wikihouseproject/Wren/Images/End-wall-01.png

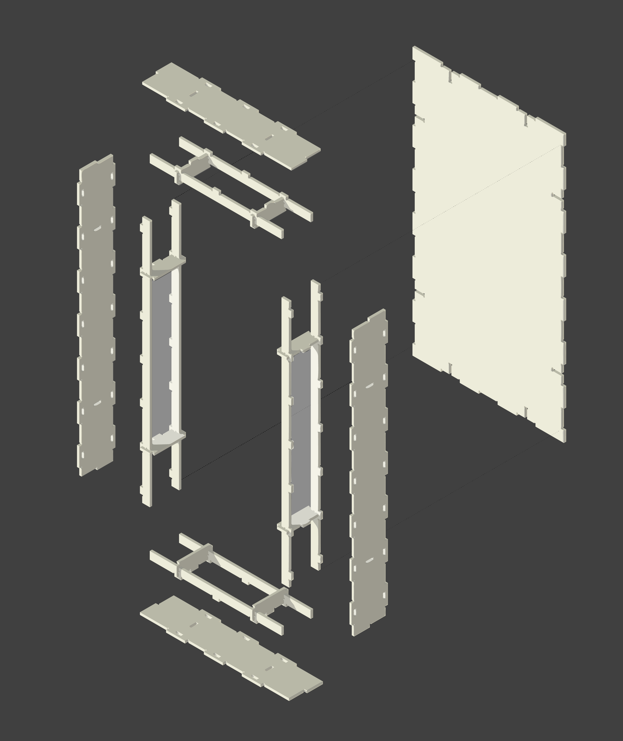
Images/End-wall-01.png
