wikihouseproject/Wren/Images/End-wall-02.png

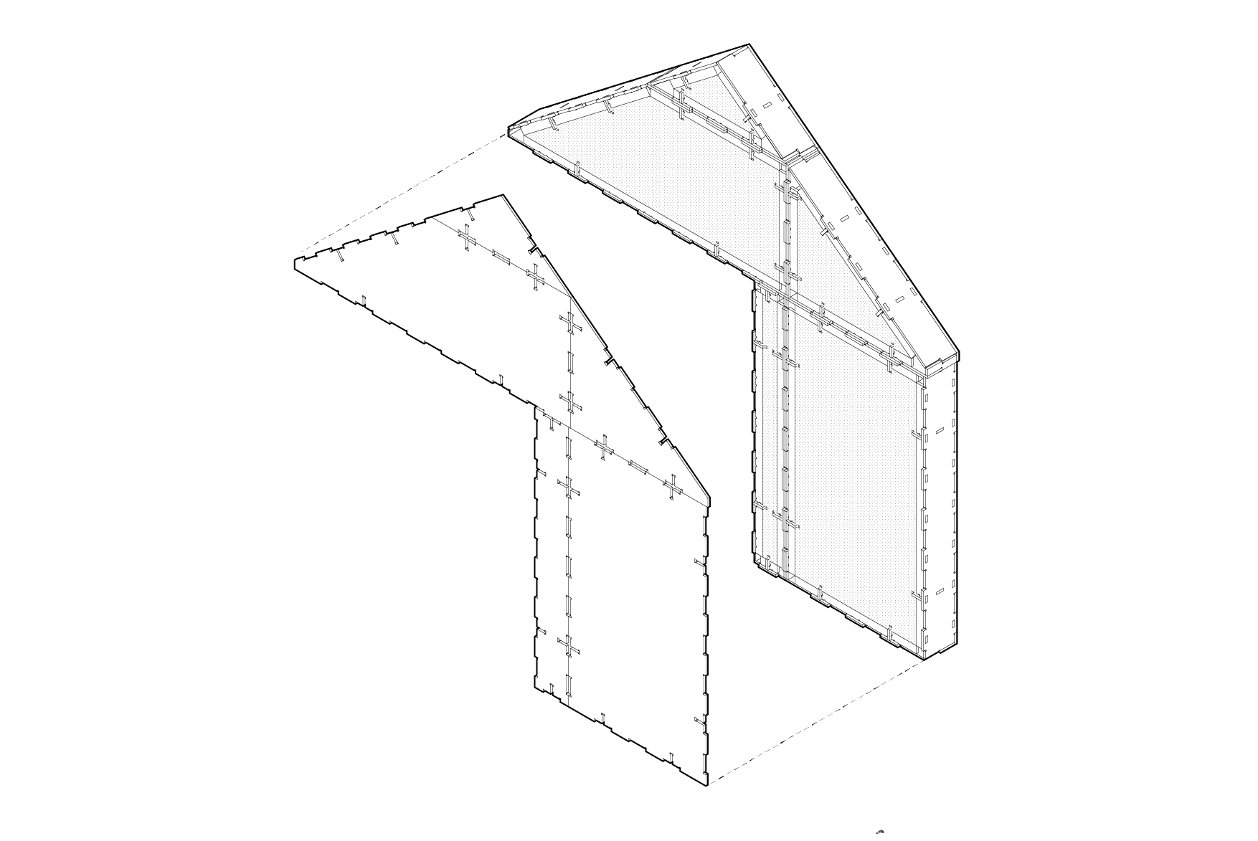
Images/End-wall-02.png
