wikihouseproject/Wren/Images/FIn-01.png

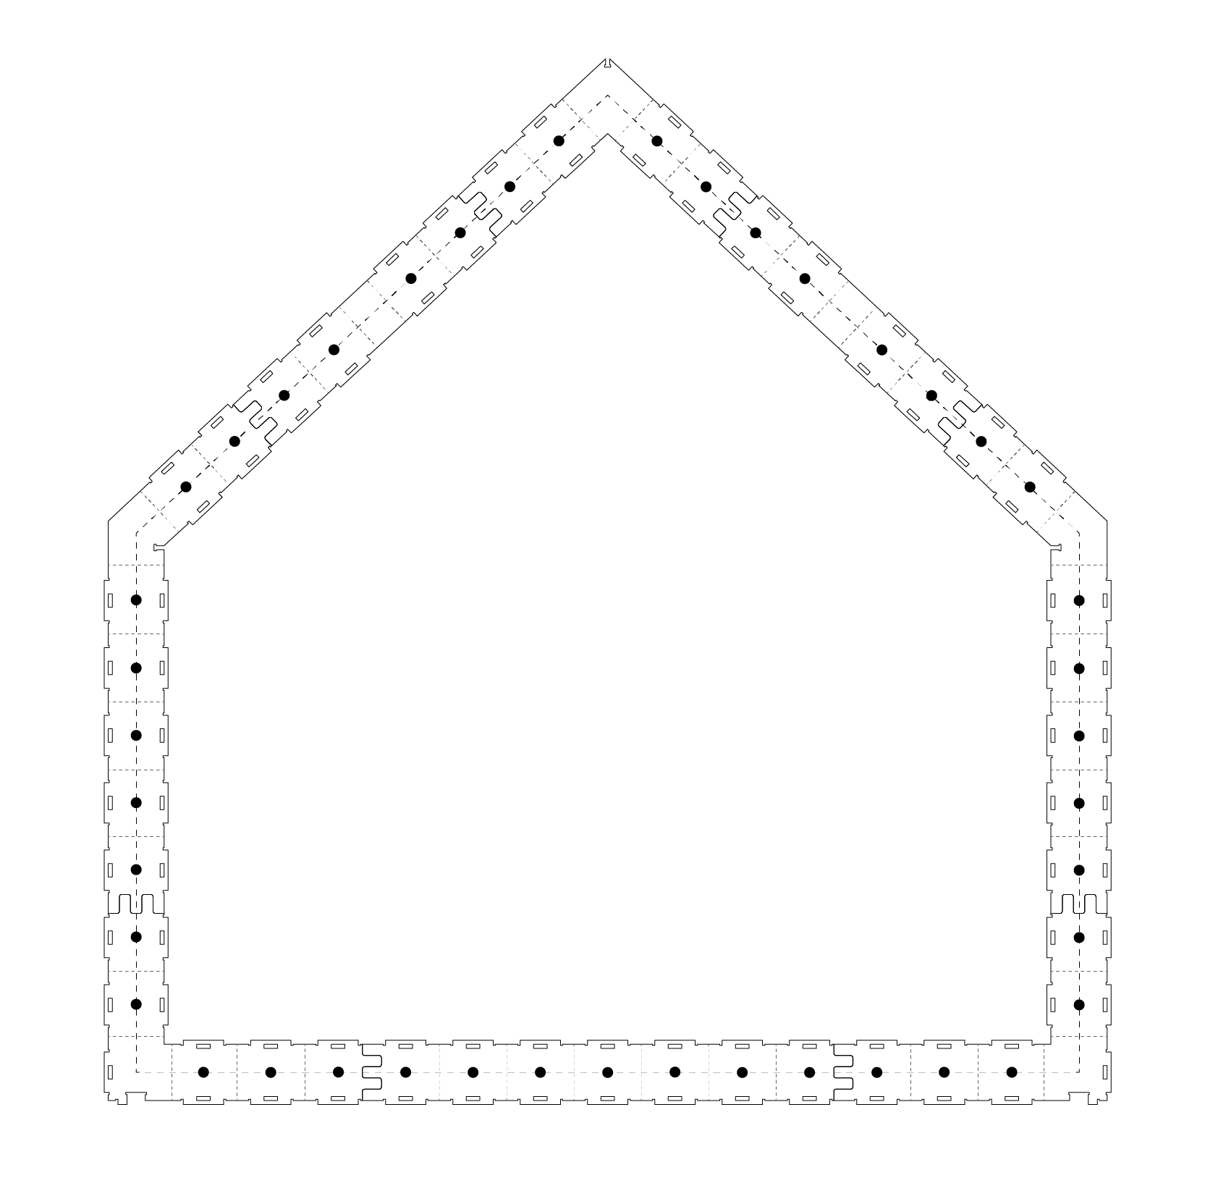
Images/FIn-01.png
