wikihouseproject/Wren/Images/Fin-02.png

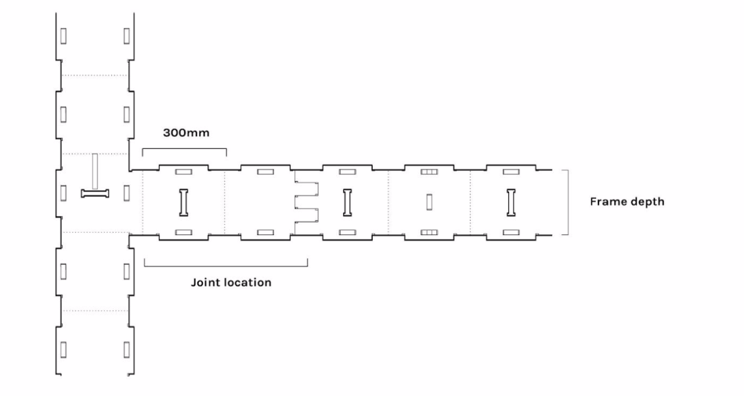
Images/Fin-02.png
