wikihouseproject/Wren/Images/Form-01.png

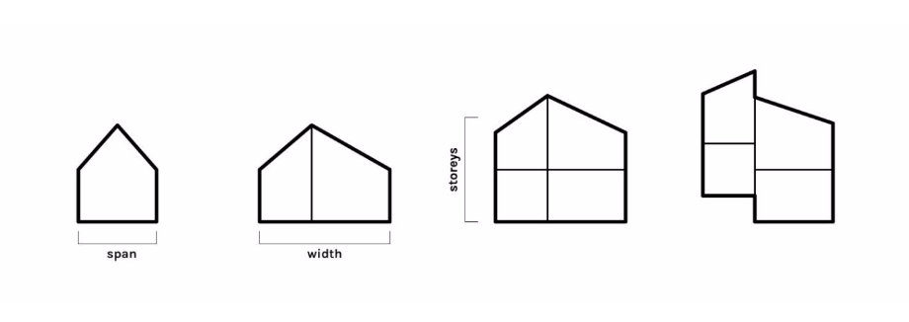
Images/Form-01.png
