wikihouseproject/Wren/Images/Frame-01.png

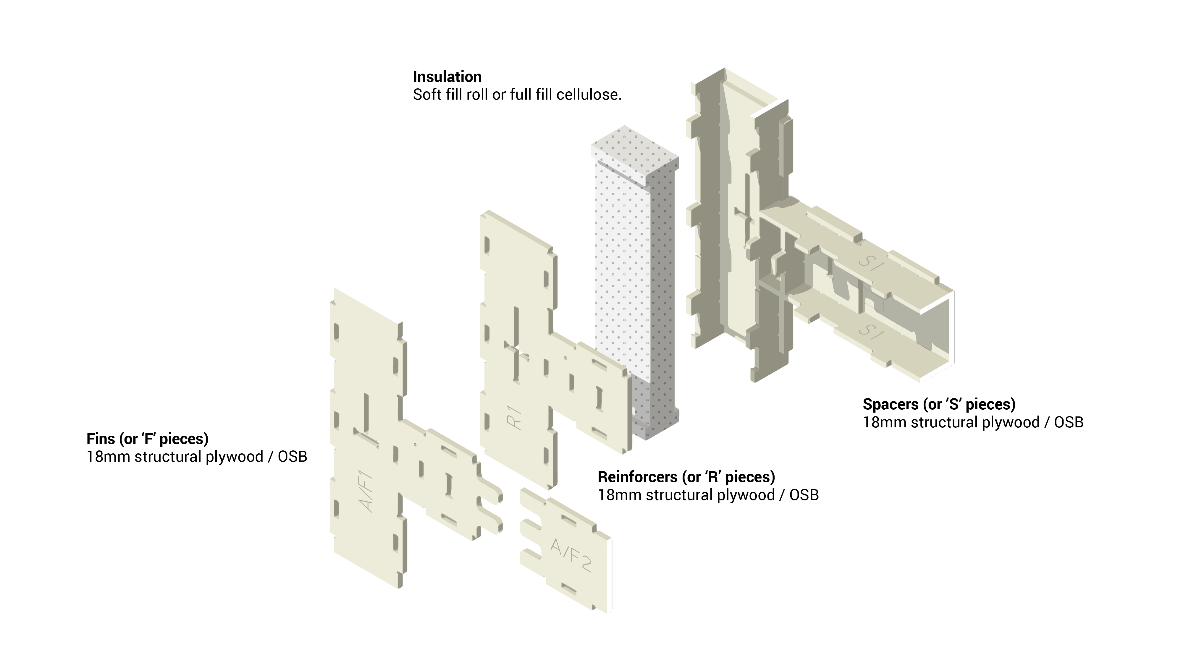
Images/Frame-01.png
