wikihouseproject/Wren/Images/Important.png

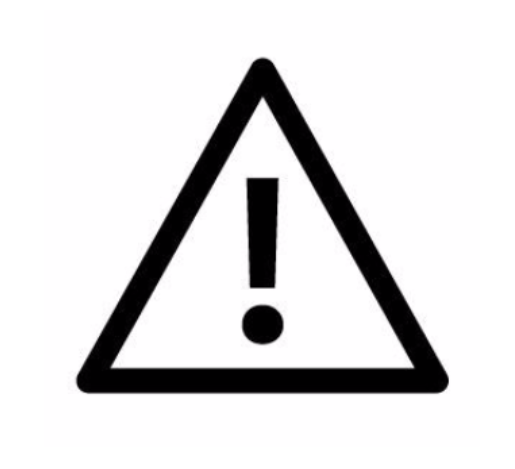
Images/Important.png
