wikihouseproject/Wren/Images/Openings-02.png

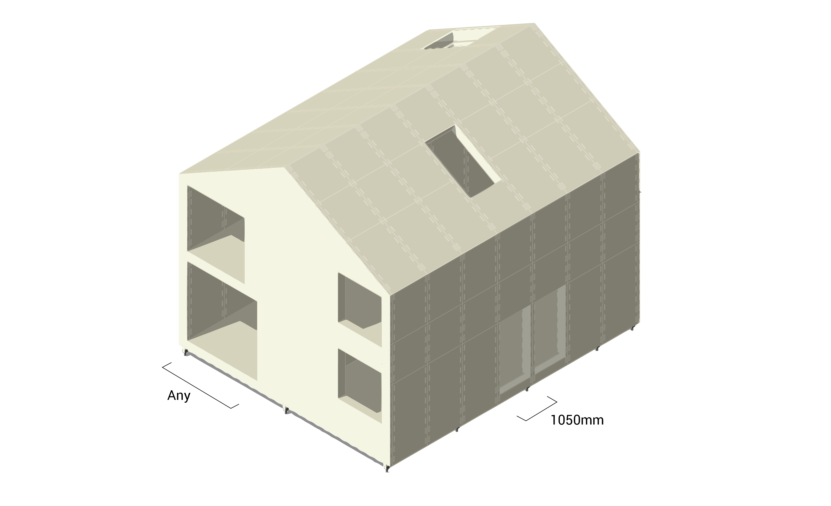
Images/Openings-02.png
