wikihouseproject/Wren/Images/Principles-01.png

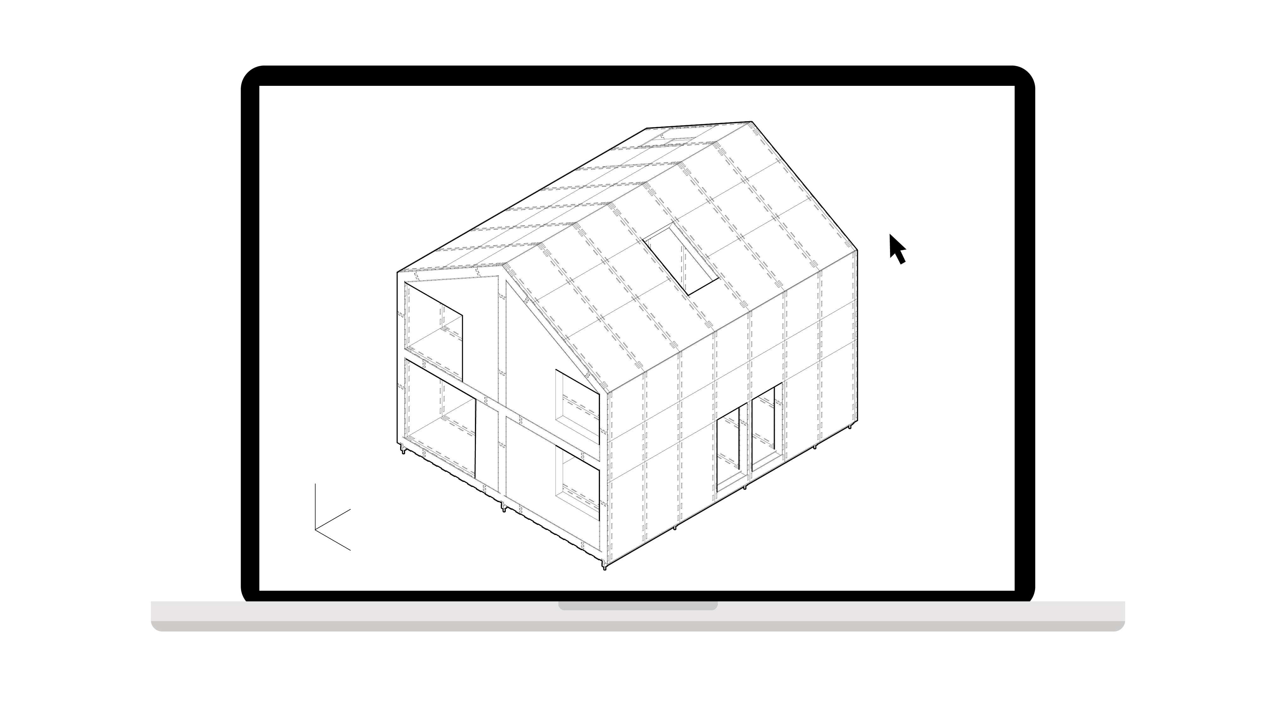
Images/Principles-01.png
