wikihouseproject/Wren/Images/Sheathing-01.png

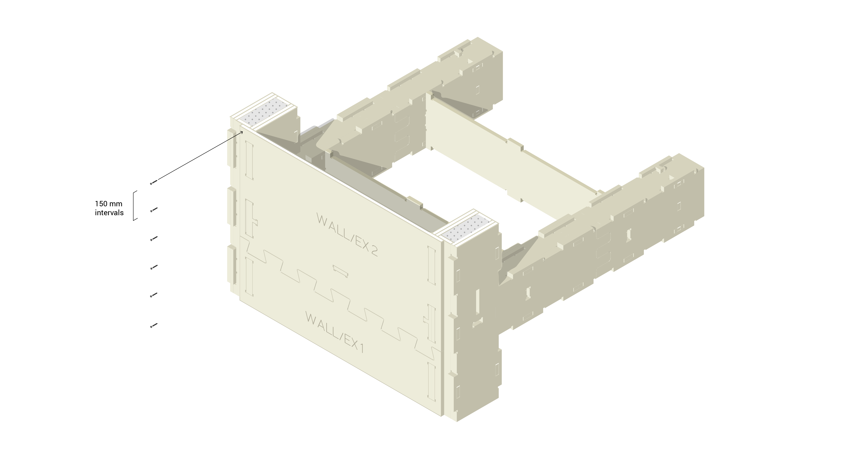
Images/Sheathing-01.png
