wikihouseproject/Wren/Images/Materials-01.png

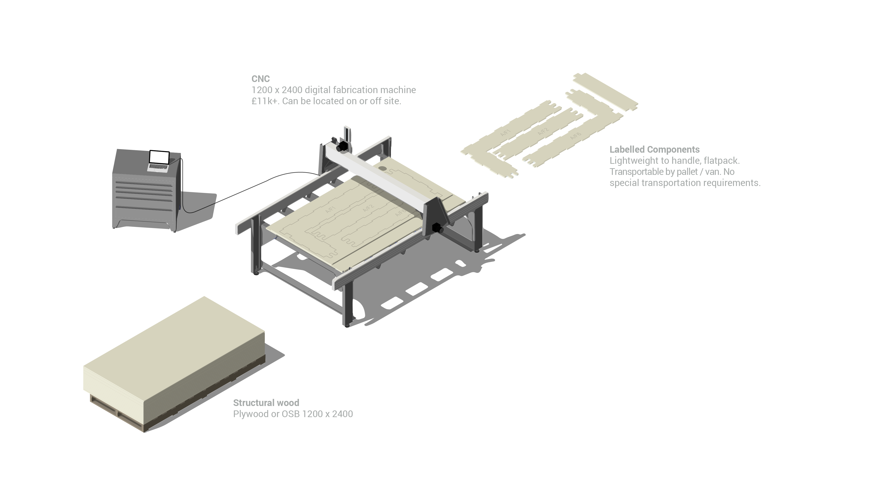
Images/Materials-01.png
