wikihouseproject/Wren/Community Build Photos/Farmhouse-01.jpg

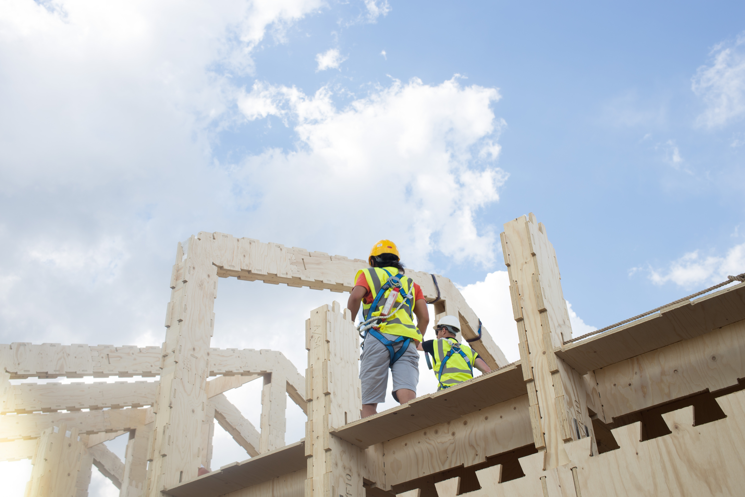
Community Build Photos/Farmhouse-01.jpg
